SuryaUT/TheM0trix_Segfaulted/Textures/circuitBoardTex.bmp

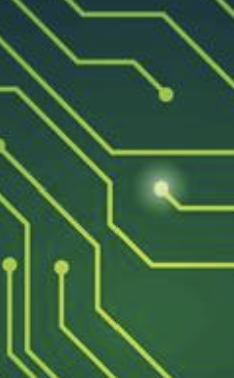
Textures/circuitBoardTex.bmp
