SuryaUT/TheM0trix_Segfaulted/Textures/matrix2.bmp

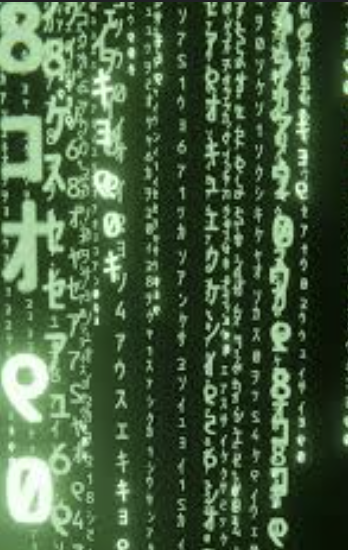
Textures/matrix2.bmp
