SuryaUT/TheM0trix_Segfaulted/Textures/SCBarkley.png

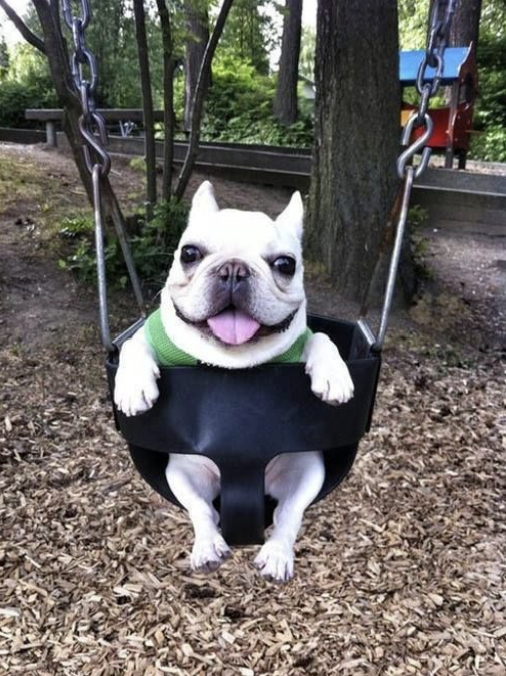
Textures/SCBarkley.png
