SuryaUT/TheM0trix_Segfaulted/images.h

// images.h
// Daniel Valvano
// March 20, 2018


#ifndef IMAGES_H
#define IMAGES_H
#include <stdint.h>

// Array for image: Ammosprite.png
const uint16_t Ammosprite[16 * 16] = {
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
};

// Array for image: ExplosionImage.png
const uint16_t ExplosionImage[32 * 32] = {
    0xFFFF, 0xFFFF, 0xFFFF, 0xFFFF, 0xFFFF, 0xFFFF, 0xFFFF, 0xFFFF, 0xFFFF, 0xFFFF, 0xFFFF, 0xFFFF, 0xFFFF, 0xFFFF, 0xFFFF, 0xFFFF, 0xFFFF, 0xFFFF, 0xFFFF, 0xFFFF, 0xFFFF, 0xFFFF, 0xFFFF, 0xFFFF, 0xFFFF, 0xFFFF, 0xFFFF, 0xFFFF, 0xFFFF, 0xFFFF, 0xFFFF, 0xFFFF, 0xFFFF, 0xFFFF, 0xFFFF, 0xFFFF, 0xFFFF, 0xFFFF, 0xFFFF, 0xFFFF, 0xFFFF, 0xFFFF, 0xFFFF, 0xFFFF, 0xFFFF, 0xFFFF, 0xFFFF, 0xFFFF, 0xFFFF, 0xFFFF, 0xFFFF, 0xFFFF, 0xFFFF, 0xFFFF, 0xFFFF, 0xFFFF, 0xFFFF, 0xFFFF, 0xFFFF, 0xFFFF, 0xFFFF, 0xFFFF, 0xFFFF, 0xFFFF, 0xFFFF, 0xFFFF, 0xFFFF, 0xFFFF, 0xFFFF, 0xFFFF, 0xFFFF, 0xFFFF, 0xFFFF, 0xFFFF, 0xFFFF, 0xFFFF, 0xFFFF, 0xFFFF, 0xFFFF, 0xF7BF, 0xF7BF, 0xFFFF, 0xFFFF, 0xFFFF, 0xFFFF, 0xFFFF, 0xFFFF, 0xFFFF, 0xFFFF, 0xFFFF, 0xFFFF, 0xFFFF, 0xFFFF, 0xFFFF, 0xFFFF, 0xFFFF, 0xFFFF, 0xFFFF, 0xFFFF, 0xFFFF, 0xFFFF, 0xFFFF, 0xFFFF, 0xFFFF, 0xFFFF, 0xFFFF, 0xFFFF, 0xFFFF, 0xFFFF, 0xFFFF, 0xFFFF, 0xB5BA, 0xB5B9, 0xFFFF, 0xFFFF, 0xFFFF, 0xFFFF, 0xFFFF, 0xFFFF, 0xFFFF, 0xFFFF, 0xFFFF, 0xFFFF, 0xFFFF, 0xFFFF, 0xFFFF, 0xFFFF, 0xFFFF, 0xFFFF, 0xFFFF, 0xFFFF, 0xFFFF, 0xFFFF, 0xFFFF, 0xFFFF, 0xFFFF, 0xEF9F, 0xFFFF, 0xFFFF, 0xFFDF, 0x9D7D, 0xEF7F, 0xFFDF, 0x5BB7, 0x5BB6, 0xFFFF, 0xE75F, 0x9D7D, 0xFFDF, 0xFFFF, 0xFFFF, 0xF79F, 0xFFFF, 0xFFFF, 0xFFFF, 0xFFFF, 0xFFFF, 0xFFFF, 0xFFFF, 0xFFFF, 0xFFFF, 0xFFFF, 0xFFFF, 0xFFFF, 0xFFFF, 0xFFFF, 0xFFFF, 0xF7BF, 0x431B, 0xA59A, 0xFFFF, 0xADDE, 0x0C1D, 0x6C7C, 0xEF5D, 0x2A96, 0x2AB6, 0xEF5D, 0x649D, 0x0C1D, 0xADDD, 0xFFFF, 0xADDE, 0x4319, 0xF79E, 0xFFFF, 0xFFFF, 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
};

// Array for image: PistolImage.png
const uint16_t PistolImage[32 * 32] = {
    0xA254, 0xA254, 0xA254, 0xA254, 0xA254, 0xA254, 0xA254, 0xA254, 0xA254, 0xA254, 0xA254, 0xA254, 0xA254, 0xA254, 0xA254, 0xA254, 0xA254, 0xA254, 0xA254, 0xA254, 0xA254, 0xA254, 0xA254, 0xA254, 0xA254, 0xA254, 0xA254, 0xA254, 0xA254, 0xA254, 0xA254, 0xA254, 0xA254, 0xA254, 0xFFFF, 0xFFFF, 0xA254, 0xA254, 0xA254, 0xA254, 0xA254, 0xA254, 0xA254, 0xA254, 0xA254, 0xA254, 0xA254, 0xA254, 0xA254, 0xA254, 0xA254, 0xA254, 0xA254, 0xA254, 0xA254, 0xA254, 0xA254, 0xA254, 0xA254, 0xA254, 0xA254, 0xA254, 0xA254, 0xA254, 0xA254, 0xFFFF, 0x2104, 0x2124, 0xFFFF, 0xA254, 0xA254, 0xA254, 0xA254, 0xA254, 0xA254, 0xA254, 0xA254, 0xA254, 0xA254, 0xA254, 0xA254, 0xA254, 0xA254, 0xA254, 0xA254, 0xA254, 0xA254, 0xA254, 0xA254, 0xA254, 0xA254, 0xA254, 0xA254, 0xA254, 0xA254, 0xA254, 0xFFFF, 0x6B4D, 0x4228, 0x4249, 0x2945, 0xFFFF, 0xA254, 0xA254, 0xA254, 0xA254, 0xA254, 0xA254, 0xA254, 0xA254, 0xA254, 0xA254, 0xA254, 0xA254, 0xA254, 0xA254, 0xA254, 0xA254, 0xA254, 0xA254, 0xA254, 0xA254, 0xA254, 0xA254, 0xA254, 0xA254, 0xA254, 0xA254, 0xFFFF, 0x39C7, 0x31A6, 0x5AEB, 0x4A69, 0x2145, 0xFFFF, 0xA254, 0xA254, 0xA254, 0xA254, 0xA254, 0xA254, 0xA254, 0xA254, 0xA254, 0xA254, 0xA254, 0xA254, 0xA254, 0xA254, 0xA254, 0xA254, 0xA254, 0xA254, 0xA254, 0xA254, 0xA254, 0xA254, 0xA254, 0xA254, 0xA254, 0xFFFF, 0x630C, 0x2124, 0x52AA, 0x3A08, 0x2945, 0x18E3, 0xFFFF, 0xA254, 0xA254, 0xA254, 0xA254, 0xA254, 0xA254, 0xA254, 0xA254, 0xA254, 0xA254, 0xA254, 0xA254, 0xA254, 0xA254, 0xA254, 0xA254, 0xA254, 0xA254, 0xA254, 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
};

// Array for image: ShotgunImage.png
const uint16_t ShotgunImage[32 * 32] = {
    0xA254, 0xA254, 0xA254, 0xA254, 0xA254, 0xA254, 0xA254, 0xA254, 0xA254, 0xA254, 0xA254, 0xA254, 0xA254, 0xA254, 0xA254, 0xA254, 0xA254, 0xA254, 0xA254, 0xA254, 0xA254, 0xA254, 0xA254, 0xA254, 0xA254, 0xA254, 0xA254, 0xA254, 0xA254, 0xA254, 0xA254, 0xA254, 0xA254, 0xA254, 0xA254, 0xA254, 0xA254, 0xA254, 0xA254, 0xA254, 0xA254, 0xA254, 0xA254, 0xA254, 0xA254, 0xA254, 0xA254, 0xA254, 0xA254, 0xA254, 0xA254, 0xA254, 0xA254, 0xA254, 0xA254, 0xA254, 0xA254, 0xA254, 0xA254, 0xA254, 0xA254, 0xA254, 0xA254, 0xA254, 0xA254, 0xA254, 0xA254, 0xA254, 0xA254, 0xA254, 0xA254, 0xA254, 0xA254, 0xA254, 0xA254, 0xA254, 0xA254, 0xA254, 0xA254, 0xA254, 0xA254, 0xA254, 0xA254, 0xA254, 0xA254, 0xA254, 0xA254, 0xA254, 0xA254, 0xA254, 0xA254, 0xA254, 0xA254, 0xA254, 0xA254, 0xA254, 0xA254, 0xA254, 0xA254, 0xA254, 0xA254, 0xA254, 0xA254, 0xA254, 0xA254, 0xA254, 0xA254, 0xA254, 0xA254, 0xA254, 0xA254, 0xA254, 0xA254, 0xA254, 0xA254, 0xA254, 0xA254, 0xA254, 0xA254, 0xA254, 0xA254, 0xA254, 0xA254, 0xA254, 0xA254, 0xA254, 0xA254, 0xA254, 0xA254, 0xA254, 0xA254, 0xA254, 0xA254, 0xA254, 0xA254, 0xA254, 0xA254, 0xA254, 0xA254, 0xA254, 0xA254, 0xA254, 0xA254, 0xA254, 0xA254, 0xA254, 0xA254, 0xA254, 0xA254, 0xA254, 0xA254, 0xA254, 0xA254, 0xA254, 0xA254, 0xA254, 0xA254, 0xA254, 0xA254, 0xA254, 0xA254, 0xA254, 0xA254, 0xA254, 0xA254, 0xA254, 0xA254, 0xA254, 0xA254, 0xA254, 0xA254, 0xA254, 0xA254, 0xA254, 0xA254, 0xA254, 0xA254, 0xA254, 0xA254, 0xA254, 0xA254, 0xA254, 0xA254, 0xA254, 0xA254, 0xA254, 0xA254, 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
};

// Array for image: RifleImage.png
const uint16_t RifleImage[32 * 32] = {
    0xA254, 0xA254, 0xA254, 0xA254, 0xA254, 0xA254, 0xA254, 0xA254, 0xA254, 0xA254, 0xA254, 0xA254, 0xA254, 0xA254, 0xA254, 0xA254, 0xA254, 0xA254, 0xA254, 0xA254, 0xA254, 0xA254, 0xA254, 0xA254, 0xA254, 0xA254, 0xA254, 0xA254, 0xA254, 0xA254, 0xA254, 0xA254, 0xA254, 0xA254, 0xA254, 0xA254, 0xA254, 0xA254, 0xA254, 0xA254, 0xA254, 0xA254, 0xA254, 0xA254, 0xA254, 0xA254, 0xA254, 0xA254, 0xA254, 0xA254, 0xA254, 0xA254, 0xA254, 0xA254, 0xA254, 0xA254, 0xA254, 0xA254, 0xA254, 0xA254, 0xA254, 0xA254, 0xA254, 0xA254, 0xA254, 0xA254, 0xA254, 0xA254, 0xA254, 0xA254, 0xA254, 0xA254, 0xA254, 0xA254, 0xA254, 0xA254, 0xA254, 0xA254, 0xA254, 0xA254, 0xA254, 0xA254, 0xA254, 0xA254, 0xA254, 0xA254, 0xA254, 0xA254, 0xA254, 0xA254, 0xA254, 0xA254, 0xA254, 0xA254, 0xA254, 0xA254, 0xA254, 0xA254, 0xA254, 0xA254, 0xA254, 0xA254, 0xA254, 0xA254, 0xA254, 0xA254, 0xA254, 0xA254, 0xA254, 0xA254, 0xA254, 0xA254, 0xA254, 0xA254, 0xA254, 0xA254, 0xA254, 0xA254, 0xA254, 0xA254, 0xA254, 0xA254, 0xA254, 0xA254, 0xA254, 0xA254, 0xA254, 0xA254, 0xA254, 0xA254, 0xA254, 0xA254, 0xA254, 0xA254, 0xA254, 0xA254, 0xA254, 0xA254, 0xA254, 0xA254, 0xA254, 0xA254, 0xA254, 0xA254, 0xA254, 0xA254, 0xA254, 0xA254, 0xA254, 0xA254, 0xA254, 0xA254, 0xA254, 0xA254, 0xA254, 0xA254, 0xA254, 0xA254, 0xA254, 0xA254, 0xA254, 0xA254, 0xA254, 0xF7FF, 0xF7FF, 0xA254, 0xA254, 0xF7FF, 0xF7FF, 0xF7FF, 0xA254, 0xA254, 0xA254, 0xA254, 0xA254, 0xA254, 0xA254, 0xA254, 0xA254, 0xA254, 0xA254, 0xA254, 0xA254, 0xA254, 0xA254, 0xA254, 0xA254, 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
};

// Array for image: RailgunImage.png
const uint16_t RailgunImage[32 * 32] = {
    0xA254, 0xA254, 0xA254, 0xFFFF, 0xFFFF, 0xA254, 0xA254, 0xA254, 0xA254, 0xA254, 0xA254, 0xA254, 0xA254, 0xA254, 0xA254, 0xA254, 0xA254, 0xA254, 0xA254, 0xA254, 0xA254, 0xA254, 0xA254, 0xA254, 0xA254, 0xA254, 0xA254, 0xA254, 0xA254, 0xA254, 0xA254, 0xA254, 0xA254, 0xA254, 0xFFFF, 0x0840, 0x0840, 0xFFFF, 0xA254, 0xA254, 0xA254, 0xA254, 0xA254, 0xA254, 0xA254, 0xA254, 0xA254, 0xA254, 0xA254, 0xA254, 0xA254, 0xA254, 0xA254, 0xA254, 0xA254, 0xA254, 0xA254, 0xA254, 0xA254, 0xA254, 0xA254, 0xA254, 0xA254, 0xA254, 0xA254, 0xFFFF, 0x0840, 0x39C5, 0x39C5, 0x0840, 0x0840, 0xFFFF, 0xA254, 0xA254, 0xA254, 0xA254, 0xA254, 0xA254, 0xA254, 0xA254, 0xA254, 0xA254, 0xA254, 0xA254, 0xA254, 0xA254, 0xA254, 0xA254, 0xA254, 0xA254, 0xA254, 0xA254, 0xA254, 0xA254, 0xA254, 0xA254, 0xA254, 0xFFFF, 0x0840, 0x1902, 0x2984, 0x39C5, 0x39C5, 0x0840, 0xFFFF, 0xFFFF, 0xA254, 0xA254, 0xA254, 0xA254, 0xA254, 0xA254, 0xA254, 0xA254, 0xA254, 0xA254, 0xA254, 0xA254, 0xA254, 0xA254, 0xA254, 0xA254, 0xA254, 0xA254, 0xA254, 0xA254, 0xA254, 0xA254, 0xA254, 0xA254, 0xFFFF, 0x0840, 0x1902, 0x2143, 0x1902, 0x39C5, 0x0840, 0x0840, 0xFFFF, 0xA254, 0xA254, 0xA254, 0xA254, 0xA254, 0xA254, 0xA254, 0xA254, 0xA254, 0xA254, 0xA254, 0xA254, 0xA254, 0xA254, 0xA254, 0xA254, 0xA254, 0xA254, 0xA254, 0xA254, 0xA254, 0xA254, 0xA254, 0xFFFF, 0x2D8A, 0x3E2D, 0x2A84, 0x4B28, 0x2984, 0x39C5, 0x18E2, 0x0840, 0xFFFF, 0xFFFF, 0xA254, 0xA254, 0xA254, 0xA254, 0xA254, 0xA254, 0xA254, 0xA254, 0xA254, 0xA254, 0xA254, 0xA254, 0xA254, 0xA254, 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
};

// Array for image: DrM0Front.png
const uint16_t DrM0Front[64 * 64] = {
    0xA254, 0xA254, 0xA254, 0xA254, 0xA254, 0xA254, 0xA254, 0xA254, 0xA254, 0xA254, 0xA254, 0xA254, 0xA254, 0xA254, 0xA254, 0xA254, 0xA254, 0xA254, 0xA254, 0xA254, 0xA254, 0xA254, 0xA254, 0xA254, 0xA254, 0xA254, 0xA254, 0xA254, 0xA254, 0xA254, 0xA254, 0xA254, 0xA254, 0xA254, 0xA254, 0xA254, 0xA254, 0xA254, 0xA254, 0xA254, 0xA254, 0xA254, 0xA254, 0xA254, 0xA254, 0xA254, 0xA254, 0xA254, 0xA254, 0xA254, 0xA254, 0xA254, 0xA254, 0xA254, 0xA254, 0xA254, 0xA254, 0xA254, 0xA254, 0xA254, 0xA254, 0xA254, 0xA254, 0xA254, 0xA254, 0xA254, 0xA254, 0xA254, 0xA254, 0xA254, 0xA254, 0xA254, 0xA254, 0xA254, 0xA254, 0xA254, 0xA254, 0xA254, 0xA254, 0xA254, 0xA254, 0xA254, 0xA254, 0xA254, 0xA254, 0xA254, 0xA254, 0xA254, 0xA254, 0xA254, 0xA254, 0xA254, 0xA254, 0x20FD, 0x20FD, 0x20FD, 0x20FD, 0x20FD, 0x20FD, 0x20FD, 0x20FD, 0xA254, 0xA254, 0xA254, 0xA254, 0xA254, 0xA254, 0xA254, 0xA254, 0xA254, 0xA254, 0xA254, 0xA254, 0xA254, 0xA254, 0xA254, 0xA254, 0xA254, 0xA254, 0xA254, 0xA254, 0xA254, 0xA254, 0xA254, 0xA254, 0xA254, 0xA254, 0xA254, 0xA254, 0xA254, 0xA254, 0xA254, 0xA254, 0xA254, 0xA254, 0xA254, 0xA254, 0xA254, 0xA254, 0xA254, 0xA254, 0xA254, 0xA254, 0xA254, 0xA254, 0xA254, 0xA254, 0xA254, 0xA254, 0xA254, 0xA254, 0xA254, 0xA254, 0xA254, 0x20FD, 0x20FD, 0x20FD, 0x0861, 0x0840, 0x1082, 0x2103, 0x18E3, 0x1081, 0x0841, 0x18C3, 0x20FD, 0x20FD, 0x20FD, 0xA254, 0xA254, 0xA254, 0xA254, 0xA254, 0xA254, 0xA254, 0xA254, 0xA254, 0xA254, 0xA254, 0xA254, 0xA254, 0xA254, 0xA254, 0xA254, 0xA254, 0xA254, 0xA254, 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
};
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
