SuryaUT/TheM0trix_Segfaulted/Soundeffects.h

// Sound effects
const uint8_t 	pistolSound[2974] = {155,172,99,62,182,182,113,115,81,109,143,146,205,191,162,147,103,125,90,73,92,97,165,110,87,139,86,89,96,65,97,142,101,47,93,122,128,131,104,103,93,102,118,85,64,71,86,79,79,98,94,114,127,83,85,122,117,96,88,115,87,60,132,117,62,117,123,90,110,106,113,119,87,86,114,110,97,100,80,70,87,70,22,37,67,59,60,39,43,47,19,22,20,23,34,30,29,19,16,18,17,19,18,19,19,18,19,18,19,18,18,18,17,17,17,16,16,15,15,14,14,13,13,12,12,12,11,11,10,10,9,9,9,8,8,8,7,7,7,7,7,8,7,8,8,7,8,7,10,18,21,28,40,53,72,86,92,101,115,132,131,139,171,169,166,184,177,184,201,195,205,217,213,213,213,212,212,212,212,212,213,213,214,215,216,217,218,219,220,222,223,224,226,227,228,230,231,232,234,235,236,237,238,240,241,242,243,243,244,245,245,245,245,244,244,244,244,244,244,244,244,244,244,244,244,243,238,232,227,222,217,212,208,203,199,195,192,188,185,182,179,177,174,172,170,169,168,166,166,165,164,164,164,164,164,165,166,166,169,168,171,172,174,178,168,174,181,172,166,157,168,172,145,147,165,147,135,146,144,139,126,126,134,117,121,114,101,108,99,115,126,104,99,93,98,105,93,79,82,94,76,53,62,56,51,71,58,50,52,54,80,64,48,62,60,72,63,49,67,73,66,58,58,63,64,77,68,65,92,85,78,85,96,99,82,110,121,98,119,117,110,131,145,142,126,134,126,127,145,124,139,156,146,145,139,150,151,164,162,138,157,155,163,175,152,147,163,172,164,161,157,166,178,177,190,181,188,200,169,186,204,193,188,176,168,163,199,201,176,191,178,186,195,169,167,175,195,185,176,186,155,156,164,152,174,176,168,163,139,134,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
127,127,127,127,128,128,128,128,128,128,128,128,128,128,128,128,128,128,128,128,128,128,128,128,128,128,128,128,128,128,128,128,128,128,128,128,128,128,128,128,128,128,128,128,128,128,128,128,128,128,128,128,128,128,128,128,128,128,128,128,128,128,128,128,128,128,128,128,128,128,128,128,128,128,128,128,128,128,128,128,128,128,128,128,128,128,128,128,128,128,128,128,128,128,128,128,128,128,128,128,128,128,128,128,128,128,128,128,128,128,128,128,128,128,128,128,128,128,128,128,128,128,128,128,128,128,128,128,128,128,128,128,128,127,127,127,127,127,127,127,127,127,127,127,127,127,127,127,127,127,127,127,127,127,127,127,127,127,127,127,127,127,127,127,127,127,127,127,127,127,128,127,128,127,128,127,127,128,127,128,127,128,127,127,128};

const uint8_t 	weaploadSound[2394] = {129,128,128,128,128,128,128,128,128,128,128,127,127,127,128,127,127,128,128,127,127,127,127,127,127,127,127,127,128,128,127,128,127,127,128,128,128,128,128,128,127,127,126,127,127,126,127,127,127,127,127,127,127,127,127,127,127,127,127,127,127,128,127,128,128,127,127,127,127,128,128,128,128,128,127,128,128,127,128,127,128,128,127,128,128,128,128,128,128,128,128,127,127,127,127,127,127,127,128,127,127,128,127,127,128,128,128,128,128,128,129,129,129,128,128,128,127,127,128,127,128,128,128,128,128,128,128,127,127,128,128,128,128,128,128,127,127,128,128,129,129,129,129,129,128,128,128,128,128,128,128,128,128,128,127,127,127,126,127,128,128,127,127,127,131,128,126,126,124,127,128,126,127,128,128,129,127,126,128,126,125,128,129,128,126,128,127,127,127,127,127,126,127,129,130,130,127,126,127,127,126,128,129,128,128,127,128,130,127,128,129,127,128,127,128,128,126,127,128,125,126,127,127,128,127,127,128,127,126,127,126,127,127,127,128,127,127,129,127,127,127,127,128,127,126,126,126,127,127,127,128,126,127,128,127,129,129,128,129,129,128,129,129,129,130,128,128,129,127,128,128,127,128,127,127,128,127,127,127,127,127,127,127,128,128,128,128,127,128,128,128,129,128,128,128,127,128,127,127,128,126,126,127,126,127,127,127,127,127,127,127,127,128,128,128,128,128,128,129,128,128,129,128,128,128,128,129,127,128,128,127,128,128,127,128,128,127,127,127,127,128,127,127,127,127,128,127,127,127,128,128,128,127,127,128,128,128,128,128,127,127,128,128,128,128,12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
7,128,127,128,127,127,128,127,127,127,127,127,128,128,128,128,128,128,128,128,127,127,128,128,127,127,127,127,128,127,127,127,128,127,127,127,128,128,128,128,128,127,128,128,128,128,128,128,128,128,128,128,127,127,128,128,127,127,127,127,127,127,127,128,128,127,127,128,128,127,127,128,127,128,127,127,127,127,127,127,127,127,127,127,127,127,127,127,127,128,127,128,128,127,127,127,127,128,127,128,128,128,127,127,127,127,128,128,128,128,127,127,128,128,128,128,128,128,127,127,127,128,128,128,127,127,127,127,127,127,128,127,127,127,127,128,128,127,128,128,127,128,128,128,128,128,128,128,127,127,128,127,128,128};
const uint8_t 	outofammoSound[2383] = {127,128,128,128,128,127,127,127,127,128,128,128,127,127,127,127,127,127,128,128,127,127,127,127,126,126,126,126,125,125,125,125,124,124,123,124,123,123,124,124,124,126,127,128,130,132,134,136,137,138,138,136,136,136,135,135,135,134,133,133,133,132,132,131,129,130,128,122,123,123,120,120,121,122,121,121,122,122,121,121,123,124,121,123,125,125,127,127,127,128,127,127,128,127,127,129,128,128,127,126,126,124,124,124,124,125,126,127,126,126,126,127,128,126,126,129,130,130,132,133,132,132,132,132,132,132,132,131,131,130,130,129,129,129,128,128,127,127,125,124,124,123,123,122,123,121,120,124,121,119,123,125,126,125,126,129,128,129,129,130,130,130,131,132,132,133,134,133,132,132,132,131,131,132,131,132,132,130,130,132,131,129,129,130,127,127,129,128,126,127,131,126,124,129,125,123,126,124,125,126,125,126,126,125,126,126,125,125,125,125,126,126,127,127,127,127,127,127,127,127,127,127,128,128,128,128,129,129,129,129,129,129,130,130,130,130,130,130,130,130,130,129,130,130,129,129,129,129,129,129,129,128,128,127,128,128,127,127,126,126,126,126,125,125,124,124,124,124,124,124,124,124,124,124,124,124,124,124,124,124,124,124,124,124,125,125,125,125,126,126,126,126,127,127,127,128,128,127,127,128,128,128,129,129,130,130,130,130,131,131,130,130,129,129,129,129,129,129,129,129,129,129,129,129,128,128,128,127,127,128,128,127,128,128,128,127,127,128,127,127,127,127,127,127,128,127,128,127,127,128,125,129,126,123,130,127,126,129,127,129,128,128,130,129,127,1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
27,127,127,127,128,127,127,128,128,128,128,128,128,127,128,128,127,128,128,128,128,127,128,128,128,128,128,128,128,127,128,127,127,128,127,127,127,127,127,127,127,127,127,127,127,127,127,128,127,127,128,128,128,128,128,128,127,127,127,127,128,128,128,128,127,128,128,127,128,127,127,128,128,127,127,127,127,127,127,127,128,128,128,128,128,128,127,127,127,127,127,127,127,127,128,127,127,128,127,127,128,128,128,128,127,127,127,127,127,127,127,127,128,128,128,127,127,127,128,127,127,127,128,128,128,128,128,128,128,128,128,128,128,127,127,128,128,128,127,128,127,127,128};

const uint8_t 	reloadSound[9152] = {127,127,128,127,127,127,127,127,127,127,127,127,127,127,127,127,127,127,127,127,127,127,127,127,127,127,127,127,128,127,127,127,127,127,128,128,127,127,127,127,128,128,128,127,127,127,127,128,128,128,127,127,127,128,128,128,127,128,128,127,128,128,127,127,127,127,128,128,128,127,127,127,127,128,128,128,127,127,128,128,128,128,128,127,127,128,128,128,128,127,128,128,128,128,128,128,128,128,127,128,128,128,127,127,127,128,128,128,127,128,128,128,128,128,128,128,128,128,128,128,128,128,128,128,128,128,128,128,128,128,128,128,128,128,128,128,128,128,128,128,128,128,128,128,128,128,128,128,128,128,128,128,128,128,128,128,128,128,128,128,128,128,129,129,128,128,128,128,128,128,128,128,128,128,128,128,128,128,128,128,128,128,128,128,128,128,128,128,128,128,128,128,128,128,128,128,128,128,128,128,128,128,128,128,128,128,128,128,128,128,128,128,128,128,128,128,128,128,128,128,128,128,128,128,128,128,128,128,128,128,128,128,128,128,128,128,128,128,128,128,127,128,127,129,127,128,129,122,132,134,122,124,127,129,131,129,128,128,125,122,130,131,128,128,125,127,129,127,129,128,125,128,128,126,128,128,128,128,127,127,129,127,127,128,127,126,127,129,128,127,127,128,127,126,127,128,127,127,128,128,127,126,127,128,128,127,128,127,127,127,127,127,127,127,127,127,127,127,127,127,127,127,127,127,127,127,127,127,127,127,127,127,127,127,127,127,127,127,127,127,127,128,127,127,127,128,127,127,127,127,127,127,127,127,127,127,127,127,127,127,127,128,127,127,127,127,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
128,128,128,128,128,128,128,128,128,128,128,128,128,128,128,128,127,128,128,128,128,128,128,127,128,128,128,128,128,127,128,128,128,128,128,127,128,128,128,128,128,127,127,128,128,127,128,127,127,128,128,128,128,128,128,127,128,128,128,128,128,128,128,128,127,128,128,128,128,128,128,128,128,127,128,128,128,128,127,128,128,128,128,128,128,128,128,128,128,128,128,128,128,128,128,128,128,128,128,128,128,128,128,128,128,128,128,128,128,128,128,128,128,127,128,128,128,128,128,128,128,128,128,128,128,128,128,128,128,128,128,128,128,128,128,128,128,128,128,128,128,128,128,128,128,128,128,127,128,127,128,127,127,127,127,128,127,128,127};
