SuryaUT/TheM0trix_Segfaulted/Textures.h

#define TEX_WIDTH 64
#define TEX_HEIGHT 64

#define CIRCUIT_BOARD_GREEN 0x06E0 // Example RGB565 color for circuit board green
#define MATRIX_GREEN 0x07E0          // Standard bright green
#define MATRIX_DARK_GREEN 0x0320    // Dark green for the "falling" effect
#define MATRIX_BACKGROUND 0x0000    // Black background
#define WIRE_COLOR1 0x05A0          // A slightly darker green
#define WIRE_COLOR2 0x04E0 
#define COMPONENT_COLOR 0x03A0      // Darker color for components
#define TRACE_COLOR 0x0770

// Array for image: circuitBoardTex.bmp
const uint16_t circuitBoardTex[64 * 64] = {
    0x39A3, 0x4183, 0x39A3, 0x2A45, 0x442B, 0x54CD, 0x3B07, 0x31A3, 0x39A3, 0x39C3, 0x39A3, 0x39C3, 0x39A3, 0x39C3, 0x39A3, 0x39C3, 0x31C3, 0x31E4, 0x4328, 0x5CEE, 0x442B, 0x2245, 0x31C3, 0x39A3, 0x39A3, 0x39C3, 0x39C3, 0x39C3, 0x39C3, 0x39C3, 0x39C3, 0x39C3, 0x39C3, 0x39C3, 0x39C3, 0x39C3, 0x39C3, 0x39C3, 0x39C3, 0x39C3, 0x39C3, 0x39C3, 0x39A3, 0x39C3, 0x31C3, 0x39C3, 0x39C3, 0x41C3, 0x41C3, 0x39C3, 0x39C3, 0x39C3, 0x39C3, 0x41C3, 0x41C3, 0x41C3, 0x39C3, 0x39C3, 0x31C3, 0x32C6, 0x5CAD, 0x54AD, 0x32A6, 0x39A3, 0x41A3, 0x41A3, 0x41C3, 0x39A3, 0x31E3, 0x4327, 0x54CD, 0x540B, 0x3265, 0x29C3, 0x31C3, 0x39C3, 0x39C3, 0x39C3, 0x39C3, 0x39C3, 0x39C3, 0x41A3, 0x39A3, 0x3285, 0x4C4C, 0x5CEE, 0x3B48, 0x2A45, 0x3A45, 0x3A45, 0x3A45, 0x3A45, 0x3A45, 0x3A45, 0x3A45, 0x3A45, 0x3A45, 0x3A45, 0x3A45, 0x3A45, 0x3A45, 0x3A45, 0x3A45, 0x3A45, 0x3A45, 0x3A45, 0x3A25, 0x3245, 0x2A24, 0x29E4, 0x39A3, 0x49A3, 0x41A3, 0x39C3, 0x39C3, 0x39C3, 0x39C3, 0x39C3, 0x41C3, 0x41C3, 0x41C3, 0x41C3, 0x41C3, 0x39C3, 0x2A04, 0x43CA, 0x54EE, 0x43AA, 0x39C3, 0x31C3, 0x31C3, 0x39C3, 0x39A3, 0x31A3, 0x3224, 0x43EA, 0x5CCE, 0x4369, 0x3204, 0x39A3, 0x41A3, 0x41C3, 0x39C3, 0x39C3, 0x39C3, 0x31C3, 0x31C3, 0x31A3, 0x31C3, 0x4307, 0x5C8D, 0x548C, 0x4C8D, 0x4C8C, 0x4C8C, 0x4C8C, 0x4C8C, 0x4C8C, 0x4C8C, 0x4C8C, 0x4C8C, 0x4C8C, 0x4C8C, 0x4C8C, 0x4C8C, 0x4C8C, 0x4C8C, 0x4C8C, 0x4C8C, 0x548C, 0x5C6C, 0x548C, 0x54CD, 0x542B, 0x3265, 0x39A3, 0x41C3, 0x31C3, 0x39C3, 0x39C3, 0x39C3, 0x39C3, 0x39C3, 0x39C3, 0x39C3, 0x39C3, 0x39C3, 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
};

// Array for image: matrix2.bmp
const uint16_t matrix2[64 * 64] = {
    0x6C4C, 0x8D70, 0x95B2, 0x95D2, 0x8DB2, 0x95B1, 0x748D, 0x2A45, 0x4B8A, 0x7CEF, 0x74CF, 0x3AE8, 0x6C8E, 0x6CAE, 0x5C0C, 0x2A87, 0x4309, 0x63ED, 0x19A4, 0x19C4, 0x2A25, 0x538A, 0x538B, 0x32A7, 0x3AA7, 0x1142, 0x1163, 0x19C4, 0x3AE8, 0x42E9, 0x1143, 0x1102, 0x1123, 0x1963, 0x1143, 0x1122, 0x0922, 0x2205, 0x6C4E, 0x4B4A, 0x19A4, 0x6C2D, 0x4B4A, 0x32A7, 0x6C2E, 0x19A4, 0x1143, 0x2A26, 0x2A05, 0x1122, 0x19C4, 0x642D, 0x8D51, 0x3246, 0x1983, 0x640D, 0x4B08, 0x21A4, 0x1922, 0x1102, 0x10E2, 0x08E2, 0x0902, 0x21A5, 0xAE94, 0xB6F6, 0xA695, 0x750F, 0x7D91, 0xAEF6, 0xAED5, 0x64AD, 0x7D50, 0x9613, 0x4BCA, 0x3B28, 0x4BEB, 0x64AD, 0x6CEE, 0x4369, 0x32A7, 0x2A87, 0x11A3, 0x53AB, 0x7CEF, 0x2A86, 0x11C4, 0x2246, 0x2A66, 0x1183, 0x19E4, 0x4329, 0x53CB, 0x538B, 0x1142, 0x0922, 0x1984, 0x4309, 0x2205, 0x0902, 0x0922, 0x1183, 0x644E, 0x4349, 0x11A3, 0x5C0C, 0x32C7, 0x4349, 0x5BCC, 0x0942, 0x0963, 0x2225, 0x19C4, 0x11A3, 0x4BCB, 0x85B1, 0x9E54, 0x4349, 0x1A04, 0x74EF, 0x6C6D, 0x19A3, 0x0902, 0x1102, 0x08E2, 0x08E2, 0x0902, 0x0902, 0xA694, 0xAED6, 0xA6B6, 0x53EB, 0x750F, 0xA6B5, 0x9EB5, 0x5C6D, 0x752F, 0x6CCE, 0x3B49, 0x4349, 0x4369, 0x5C0C, 0x3B28, 0x5C0B, 0x3B28, 0x32C7, 0x11A3, 0x4369, 0x8D92, 0x644D, 0x3B29, 0x2A86, 0x32C7, 0x1183, 0x19C4, 0x19E4, 0x4BAA, 0x4B49, 0x1162, 0x1163, 0x1143, 0x3AA8, 0x1163, 0x0902, 0x0902, 0x1183, 0x4309, 0x1163, 0x0942, 0x42E8, 0x3B08, 0x4B6A, 0x2A46, 0x0942, 0x1183, 0x640D, 0x3266, 0x0962, 0x5C2C, 0xA6D5, 0xAED5, 0x95D2, 0x11C3, 0x3B08, 0x5C0C, 0x2225, 0x0922, 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
};

// Array for image: SCBarkley.png
const uint16_t SCBarkley[64 * 64] = {
    0x9451, 0xCE59, 0xFFFF, 0xE6FB, 0x62EB, 0x3145, 0x41C6, 0x62CA, 0x836D, 0x5B2B, 0x7B4C, 0x5289, 0x4268, 0x4268, 0x4288, 0x840F, 0xB596, 0x2924, 0xA4F3, 0xBDD7, 0x2965, 0x73EE, 0x638C, 0x52EA, 0x42C9, 0x3AEA, 0x74D1, 0xC699, 0x4A49, 0x3A89, 0x3AC9, 0x3247, 0x73CE, 0xCE79, 0xC658, 0x94F3, 0x52AA, 0x3125, 0xC638, 0xFFFF, 0x5AAB, 0x20E4, 0x2945, 0x2945, 0x3145, 0x2945, 0x2925, 0x2924, 0x2104, 0x20E3, 0x5BCD, 0x6C90, 0x74F2, 0xAF1A, 0x6BAE, 0x41A6, 0x6249, 0x72AA, 0x41E7, 0x3145, 0x2945, 0x7CB1, 0x6C4F, 0x42C9, 0xDEBA, 0x734D, 0xB575, 0xC617, 0x73CD, 0x3986, 0x3965, 0x5269, 0x834C, 0x738D, 0x83AD, 0x5268, 0x4AA9, 0x4288, 0x3A27, 0x6BAD, 0x9CF3, 0x2945, 0x630B, 0xBDF7, 0x31C7, 0x4289, 0x5BAC, 0x4ACA, 0x3A28, 0x29E6, 0x7CB1, 0x94F3, 0x29A6, 0x5C0E, 0x434B, 0x430A, 0x5B8C, 0x9D13, 0xE71C, 0xB5D6, 0x4269, 0x3165, 0xDEBA, 0xFFDF, 0x4A29, 0x2904, 0x2945, 0x2924, 0x2945, 0x2924, 0x2924, 0x2104, 0x20E3, 0x18E3, 0x4B4C, 0x6D12, 0x8DF5, 0x85F5, 0x6B4C, 0x6249, 0x6269, 0x5A49, 0x41A7, 0x2904, 0x31E7, 0x84D2, 0x5BAD, 0x53CD, 0xFFDE, 0xDEFB, 0x62CB, 0x630B, 0x6BEE, 0x4228, 0x3166, 0x41E7, 0x6B4C, 0x8BAE, 0x5227, 0x52C9, 0x4288, 0x4288, 0x4268, 0x52EA, 0x4268, 0x2965, 0x3A47, 0x6C0E, 0x3A27, 0x29C6, 0x536C, 0x5B4C, 0x4A28, 0x2986, 0x4B0B, 0x31E7, 0x42A9, 0x438B, 0x432B, 0x434B, 0x430A, 0x9512, 0xC638, 0xCE79, 0x41E8, 0x2945, 0xB617, 0xE77D, 0x4A28, 0x2104, 0x2924, 0x2924, 0x2945, 0x2924, 0x2924, 0x2924, 0x20E3, 0x18A3, 0x6C2F, 0xA6F9, 0x9636, 0x6CD1, 0x734C, 0x6249, 0x49C6, 0x4A08, 0x41A7, 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
};

const uint16_t* textures[] = {circuitBoardTex, matrix2, SCBarkley, circuitBoardTex};
