SuryaUT/TheM0trix_Segfaulted/Sync.c

// Manages synchronization between player states through UART

#include "Sync.h"
#include "FIFO.h"
#include "UART1.h"
#include "UART2.h"
#include "sprites.h"
#include "../inc/Timer.h"
#include "../inc/Clock.h"
#include "ti/devices/msp/msp.h"
#include "Graphics.h"
#include <stdlib.h>
#include <math.h>
#include "SoundSD.h"

extern Sprite Sprites[];
Sprite* otherPlayer = Sprites;
extern uint8_t healthCode;
uint8_t itemsStatus = 1;
extern const uint16_t DrM0Front[];
extern const uint16_t DrM0Back[];
extern const uint16_t AgentYFront[];
extern const uint16_t AgentYBack[];
extern uint8_t worldMap[MAP_WIDTH][MAP_HEIGHT];
extern int numsprites;
extern uint8_t isPlaying;

HitDir_t  hitDir   = HIT_FRONT;
uint16_t  hitTimer = 0;

static void ComputeHitDirection(void){
  // vector from you → attacker
  double ax = other.posX - self.posX;
  double ay = other.posY - self.posY;
  // dot products against your forward/right axes
  double fwd = ax*self.dirX + ay*self.dirY;        // how much in front
  double sid = ax*self.dirY - ay*self.dirX;        // positive = attacker is to your right

  // pick the largest magnitude axis
  if (fabs(fwd) >= fabs(sid)) {
    hitDir = (fwd >= 0) ? HIT_FRONT : HIT_BACK;
  } else {
    hitDir = (sid >= 0) ? HIT_RIGHT : HIT_LEFT;
  }
}


void getRandomMapPos(uint8_t* x, uint8_t* y){
  uint8_t randX = (rand() % (MAP_WIDTH-2)) + 1;
  uint8_t randY = (rand() % (MAP_HEIGHT-2)) + 1;

  while (worldMap[randX][randY] != 0){
    randX = (rand() % (MAP_WIDTH-2)) + 1;
    randY = (rand() % (MAP_HEIGHT-2)) + 1;
  }

  *x = randX;
  *y = randY;
}

void RandomizeSprites(){ // Will randomize sprite positions and synchronize
  for (int i = 1; i < numsprites; i++){
    if (IS_DOMINANT_CONTROLLER){
      uint8_t x, y;
      getRandomMapPos(&x, &y);
      Sprites[i].x = x + .5;
      Sprites[i].y = y + .5;
      UART1_OutChar('{');
      UART1_OutChar(x);
      UART1_OutChar(y);
    }
    else{
      while (UART2_InChar() != '{') {}
      Sprites[i].x = UART2_InChar() + .5;
      Sprites[i].y = UART2_InChar() + .5;
    }
    Sprites[i].width = 0; // Reset item so it has to spawn to appear
    Clock_Delay1ms(50);
  }

  // Now arm synchronization interrupts
  TimerG8_IntArm(1000000/128, 128, 1);
  TimerG7_IntArm(400000/128, 128, 2);
  TimerA0_IntArm(40000, 200, 3);
}

void handshake(){
  TimerA1_IntArm(400000/128, 128, 2);
  needSync = 1;
  while (UART2_InChar0() != 'M'){SoundSD_Service();}
  friendlyDelay(10);
  needSync = 0;
  NVIC->ICER[0] = (1<<19);
}

void Sync_Init(){
  UART1_Init();
  UART2_Init();
}

uint8_t getPositionPacket(){
  if (RxFifo_Size() < 4) return 0;
  while (UART2_InChar() != '<'){}
  uint8_t inX = UART2_InChar();
  uint8_t inY = UART2_InChar();
  uint8_t endSentinel = UART2_InChar();
  if (endSentinel == '>'){
    otherPlayer->x = inX/10.0;
    otherPlayer->y = inY/10.0;
    other.posX = otherPlayer->x;
    other.posY = otherPlayer->y;
  }
  return 1;
}

#define COS0    0.5       // cosine of half‑angle (e.g. 60° → 0.5)
#define COS02   (COS0*COS0)
uint8_t getDirectionPacket(){
  if (RxFifo_Size() < 4) return 0;
  while (UART2_InChar() != '[') {}

  int8_t rawDirX = UART2_InChar();
  int8_t rawDirY = UART2_InChar();
  uint8_t endSentinel = UART2_InChar();

  if (endSentinel == ']') {
    // reconstruct their forward‐vector (≈ unit length)
    other.dirX = rawDirX / 100.0;
    other.dirY = rawDirY / 100.0;

    // vector from them → you
    double vx = self.posX - other.posX;
    double vy = self.posY - other.posY;

    // raw dot = |D|·|V|·cosθ
    double dot   = other.dirX * vx + other.dirY * vy;
    double dist2 = vx*vx + vy*vy;

    // front half‐plane & within ±60° cone?
    if ( dot > 0.0
      && dot*dot > COS02 * dist2 )
    {
      otherPlayer->image = IS_DOMINANT_CONTROLLER
        ? DrM0Front
        : AgentYFront;
    } else {
      otherPlayer->image = IS_DOMINANT_CONTROLLER
        ? DrM0Back
        : AgentYBack;
    }
  }
  return 1;
}

void processHit(int damage){
  if (!self.isVulnerable) return;
  ComputeHitDirection();
  hitTimer = HIT_INDICATOR_DURATION;
  self.playerHealth -= damage;
}


uint8_t getInfoPacket(){
  if (RxFifo_Size() < 4) return 0;
  while (UART2_InChar() != '('){}
  uint8_t inHealthCode = UART2_InChar();
  uint8_t inItemsStatus = UART2_InChar();
  uint8_t endSentinel = UART2_InChar();
  if (endSentinel == ')'){
    switch (inHealthCode){
      case PISTOLCODE: processHit(2); break;
      case SHOTGUNCODE: processHit(15); break;
      case RIFLECODE: processHit(3); break;
      case MEDKITCODE: other.playerHealth += 20; if (other.playerHealth > 50) other.playerHealth = 50; break;
      case RESPAWNCODE: other.playerHealth = 50; self.kills++; break;
      case DEADCODE: processHit(50); break;
      case RESTARTCODE: isPlaying = 0; break;
    }
    uint8_t itemCode = (inItemsStatus >> 6) & 3; // Get top two bits for event code
    uint8_t sprite_index = inItemsStatus & 0xF; // Get bottom four bits for index of sprite to alter
    if (itemCode == PICKUPCODE){
      Sprites[sprite_index].width = 0;
    }
    else if (itemCode == SPAWNCODE){
      Sprites[sprite_index].width = Sprites[sprite_index].height;
    }
  }
  return 1;
}

void sendPositionPacket(){
  uint8_t sendX = (uint8_t) ((self.posX+0.05)*10);//convert into fixed point
  uint8_t sendY = (uint8_t) ((self.posY+0.05)*10);//convert into fixed point

  UART1_OutChar('<');
  UART1_OutChar(sendX);
  UART1_OutChar(sendY);
  UART1_OutChar('>');
}

void sendDirectionPacket(){
  int8_t sendX = (int8_t) ((self.dirX+.005)*100);//convert into fixed point
  int8_t sendY = (int8_t) ((self.dirY+.005)*100);//convert into fixed point

  UART1_OutChar('[');
  UART1_OutChar(sendX);
  UART1_OutChar(sendY);
  UART1_OutChar(']');
}

void sendInfoPacket(){
  UART1_OutChar('(');
  UART1_OutChar(healthCode);
  UART1_OutChar(itemsStatus);
  UART1_OutChar(')');
  healthCode = 1; // 1 means do nothing
  itemsStatus = 1; // 1 means do nothing
}

 void TIMG8_IRQHandler(void){
  if((TIMG8->CPU_INT.IIDX) == 1){ // this will acknowledge
    static uint8_t packetIndex = 0;
    if (packetIndex == 0) sendPositionPacket();
    else if (packetIndex == 1) sendDirectionPacket();
    else if (packetIndex == 2) sendInfoPacket();
    else{
      packetIndex = -1; // Will be set to 0 in the next line
    }
    packetIndex++;
  }
}

 void TIMG7_IRQHandler(void){
  if((TIMG7->CPU_INT.IIDX) == 1){ // this will acknowledge
    static uint8_t packetIndex = 0;
    if (packetIndex == 0) packetIndex += getPositionPacket();
    else if (packetIndex == 1) packetIndex += getDirectionPacket();
    else if (packetIndex == 2) packetIndex += getInfoPacket();
    else packetIndex = 0;
  }
}

#define RESPAWN_TIME 30

void TIMA0_IRQHandler(void){ // Spawn new item every 30 seconds
  static uint16_t timeCt = 1;
  if((TIMA0->CPU_INT.IIDX) == 1){ // this will acknowledge
    if(timeCt == 0) generateSprite();
    timeCt = (timeCt + 1) % (RESPAWN_TIME*10);
  }
}
