SuryaUT/TheM0trix_Segfaulted/Sounds.c

#include "ti/devices/msp/m0p/mspm0g350x.h"
#include "../inc/DAC.h"
#include <stdint.h>
#include "Sounds.h"
#include "Soundeffects.h"

uint32_t Length;
const uint8_t* SoundPt;
uint8_t SoundMode = 0;
uint8_t enabled = 0;

sound_t SoundEffects[] = {
  {pistolSound, 2794},
  {shotgunSound, 7800},
  {weaploadSound, 2394},
  {outofammoSound, 2383},
  {reloadSound, 9152}
};

void SoundEffects_enable(){
  enabled = 1;
  SoundMode = 0;
}

void SoundEffects_disable(){
  enabled = 0;
  SoundMode = 1;
}

void Sound_Init(uint32_t period, uint32_t priority){
  DAC_Init();
  SysTick->CTRL = 0; // Disable SysTick
  SysTick->LOAD = period-1; // Reload Value
  SysTick->VAL = 0; // Clear
  SCB->SHP[1] = (SCB->SHP[1] & ~0xC0000000) | priority << 30; // Set priority
  SysTick->CTRL = 0x0007; // Enable SysTick with core clock and interrupts
}

void Sound_Start(sound_t sound){
    if (!enabled) return;
    Length = sound.Length;
    SoundPt = sound.SoundPt;
    SysTick->LOAD = 80000000/11000-1;
    SysTick->VAL = 0;
}
