SuryaUT/TheM0trix_Segfaulted/Sounds.h

#ifndef __SOUNDS_H__
#define __SOUNDS_H__

extern const uint8_t 	pistolSound[2974];
extern const uint8_t 	shotgunSound[7800];
extern const uint8_t 	weaploadSound[2394];
extern const uint8_t 	outofammoSound[2383];
extern const uint8_t 	reloadSound[9152];

extern uint8_t SoundMode;

#define PISTOL_SOUND 0
#define SHOTGUN_SOUND 1
#define WEAPLOAD_SOUND 2
#define OUTOFAMMO_SOUND 3
#define RELOAD_SOUND 4

typedef struct{
  const uint8_t *SoundPt;
  uint32_t Length;
} sound_t;


extern sound_t SoundEffects[];

void Sound_Init(uint32_t period, uint32_t priority);
void Sound_Start(sound_t sound);
void SoundEffects_enable();
void SoundEffects_disable();


#endif
